longyuxi/2019-genas-china-smart-device/TSL2561.py

import smbus
import time
 
# Get I2C bus
bus = smbus.SMBus(1)
 
bus.write_byte_data(0x39, 0x00 | 0x80, 0x03)
bus.write_byte_data(0x39, 0x01 | 0x80, 0x02)
 
time.sleep(0.5)

data = bus.read_i2c_block_data(0x39, 0x0C | 0x80, 2)
data1 = bus.read_i2c_block_data(0x39, 0x0E | 0x80, 2)

def readRaw():
    global data
    global data1 
    data = bus.read_i2c_block_data(0x39, 0x0C | 0x80, 2)
    data1 = bus.read_i2c_block_data(0x39, 0x0E | 0x80, 2)
 
# Convert the data


def fullSpectrumValue():
    readRaw()
    ch0 = data[1] * 256 + data[0]
    ch1 = data1[1] * 256 + data1[0]
    return ch0

def IRValue():
    readRaw()
    ch0 = data[1] * 256 + data[0]
    ch1 = data1[1] * 256 + data1[0]
    return ch1

def visibleValue():
    return fullSpectrumValue() - IRValue()
